matthieuvigne/MiAM_eurobot2018/Code_BBB/EurobotCode/src/Robot.c

#include "Robot.h"

// Define robot constants.
const double STEP_TO_SI = G_PI * 90.0 / 400.0;

const double ROBOT_WIDTH = 340;
const double CHASSIS_BACK = 145;
const double CHASSIS_FRONT = 145;
const double CHASSIS_SIDE = 155;
const double CANON_OFFSET = 103;
const double CLAW_OFFSET = 120;
const double MOUSE_SENSOR_OFFSET = 110;
const double BALL_LENGTH_OFFSET = 156;
const double BALL_WIDTH_OFFSET = 29;
const double BIN_OFFSET = 105;

const double GYRO_Z_BIAS = -0.00002;

const int RIGHT = 1;
const int LEFT = 0;

RobotPosition startingPosition = {0,0,0};

// Implementation of thread-safe robotPosition position and robotPosition target.
RobotPosition robotPosition;
GMutex positionMutex;

double robot_getPositionX()
{
	g_mutex_lock(&positionMutex);
	double x = robotPosition.x;
	g_mutex_unlock(&positionMutex);
	return x;
}

double robot_getPositionY()
{
	g_mutex_lock(&positionMutex);
	double Y = robotPosition.y;
	g_mutex_unlock(&positionMutex);
	return Y;
}

double robot_getPositionTheta()
{
	g_mutex_lock(&positionMutex);
	double t = robotPosition.theta;
	g_mutex_unlock(&positionMutex);
	return t;
}

void robot_setPositionX(double x)
{
	g_mutex_lock(&positionMutex);
	robotPosition.x = x;
	g_mutex_unlock(&positionMutex);
}

void robot_setPositionY(double y)
{
	g_mutex_lock(&positionMutex);
	robotPosition.y = y;
	g_mutex_unlock(&positionMutex);
}

void robot_setPositionTheta(double t)
{
	g_mutex_lock(&positionMutex);
	robotPosition.theta = t;
	g_mutex_unlock(&positionMutex);
}

void robot_setPosition(RobotPosition pos)
{
	g_mutex_lock(&positionMutex);
	robotPosition.x = pos.x;
	robotPosition.y = pos.y;
	robotPosition.theta = pos.theta;
	g_mutex_unlock(&positionMutex);
}

RobotPosition robot_getPosition()
{
	RobotPosition pos;
	g_mutex_lock(&positionMutex);
	pos.x = robotPosition.x;
	pos.y = robotPosition.y;
	pos.theta = robotPosition.theta;
	g_mutex_unlock(&positionMutex);
	return pos;
}
