matthieuvigne/MiAM_eurobot2018/Code_BBB/BBBEurobot/src/TCS3472ColorSensorDriver.c

#include "BBBEurobot/TCS3472ColorSensorDriver.h"
#include <math.h>
#include <stdio.h>

// Slave address: constant by chip reference.
// For TCS34725 and TCS34727 use 0x29.
// For TCS34721 and TCS34723 use 0x39.
const guint8 TCS3472_ADDRESS = 0x29;

const guint8 TCS3472_COMMAND_BIT = 0x80;

gboolean colorSensor_init(ColorSensorTCS3472 *sensor, I2CAdapter *adapter)
{
	if(adapter->file < 0)
		return FALSE;
	sensor->adapter = adapter;
	// Check chip identity.
	guint8 chipIdentity = i2c_readRegister(sensor->adapter, TCS3472_ADDRESS, TCS3472_COMMAND_BIT | 0x12);
	if(chipIdentity != 0x44 && chipIdentity != 0x4D)
	{
		printf("Error : TCS3472 not detected\n");
		return FALSE;
	}
	// Configure chip.
	// Set command register
	i2c_writeRegister(sensor->adapter, TCS3472_ADDRESS, TCS3472_COMMAND_BIT | 0x00, 0b10100000);

	// Set default integration time and gain.s
	colorSensor_setIntegrationTime(*sensor, 3);
	colorSensor_setGain(*sensor, TCS34725_GAIN_1X);
	// Enable chip.
	i2c_writeRegister(sensor->adapter, TCS3472_ADDRESS, TCS3472_COMMAND_BIT | 0x00, 0x01);
	// Wait 3ms for oscillator to start, then powerup the device.
	g_usleep(3000);
	i2c_writeRegister(sensor->adapter, TCS3472_ADDRESS, TCS3472_COMMAND_BIT | 0x00, 0x03);
	return TRUE;
}


gboolean colorSensor_setIntegrationTime(ColorSensorTCS3472 sensor, int integrationTime)
{
	// Compute register value.
	guint8 registerValue = (guint8) (256 - (floor(integrationTime / 2.4)));
	return i2c_writeRegister(sensor.adapter, TCS3472_ADDRESS, TCS3472_COMMAND_BIT | 0x01, registerValue);
}

gboolean colorSensor_setGain(ColorSensorTCS3472 sensor, TCS34725Gain_t gain)
{
	return i2c_writeRegister(sensor.adapter, TCS3472_ADDRESS, TCS3472_COMMAND_BIT | 0x0F, gain);
}

ColorOutput colorSensor_getData(ColorSensorTCS3472 sensor)
{
	ColorOutput color;
	guint8 sensorValue[8];
	i2c_readRegisters(sensor.adapter, TCS3472_ADDRESS, TCS3472_COMMAND_BIT | 0x14, 8, sensorValue);
	color.clear = (sensorValue[0] << 8) + sensorValue[1];
	color.red = (sensorValue[2] << 8) + sensorValue[3];
	color.green = (sensorValue[4] << 8) + sensorValue[5];
	color.blue = (sensorValue[6] << 8) + sensorValue[7];

	return color;
}
