matthieuvigne/MiAM_eurobot2018/Code_BBB/BBBEurobot/include/BBBEurobot/ADNS9800Firmware.h

// the firmeware that is uploaded in the ADNS each time it boots
#ifndef ADNS9800_FIRMWARE
#define ADNS9800_FIRMWARE
// Firmware "adns9800_srom_A4.txt" from 
// This firmware is Copyright Avago, please refer to them concerning modifications.

	const unsigned short firmware_length = 3070;
	uint8_t firmware_data[] = {
	0x03, 0xa4, 0x6e, 0x16, 0x6d, 0x89, 0x3e, 0xfe, 0x5f, 0x1c, 0xb8, 0xf2, 0x47, 0x0c, 0x7b, 
	0x74, 0x6a, 0x56, 0x0f, 0x7d, 0x76, 0x71, 0x4b, 0x0c, 0x97, 0xb6, 0xcf, 0xfd, 0x78, 0x72, 
	0x66, 0x2f, 0xbd, 0xf8, 0x53, 0x24, 0xab, 0xd4, 0x2c, 0xb0, 0xe4, 0x32, 0xf1, 0x6a, 0x56, 
	0x2e, 0xbf, 0xfc, 0x7a, 0x57, 0x0d, 0x79, 0x70, 0x66, 0x46, 0x0e, 0x7f, 0x5d, 0x19, 0x91, 
	0xaa, 0xc2, 0x0d, 0x8e, 0x7f, 0x5d, 0x19, 0xb0, 0xe2, 0x46, 0xef, 0x5c, 0x3a, 0xd7, 0x2c, 
	0xbb, 0xf4, 0x6a, 0x37, 0xcd, 0x18, 0xb2, 0xc7, 0x0c, 0x9a, 0x97, 0x8f, 0x52, 0xfd, 0x0d, 
	0xb8, 0x41, 0x00, 0x9e, 0x8e, 0x9a, 0x1e, 0x6d, 0x0c, 0xe2, 0xaa, 0x13, 0x93, 0xb8, 0xc1, 
	0x2a, 0x29, 0xbb, 0x0b, 0xe3, 0x71, 0x08, 0x6d, 0xfd, 0xb6, 0xd9, 0xcf, 0x65, 0x21, 0x27, 
	0x45, 0x1b, 0xbe, 0xe2, 0x61, 0x86, 0x3c, 0xbf, 0x68, 0x9c, 0xd6, 0x75, 0x01, 0x5e, 0xe0, 
	0xc6, 0x92, 0x79, 0xf4, 0x6a, 0xa9, 0xbb, 0x2a, 0x79, 0xd0, 0xe1, 0x5c, 0x32, 0xb1, 0x5a, 
	0x1b, 0xba, 0xaf, 0x11, 0xea, 0x24, 0x6a, 0x83, 0x4f, 0x8d, 0xed, 0x19, 0x62, 0x70, 0x54, 
	0xfb, 0x0e, 0x1f, 0x83, 0xcc, 0xf0, 0xb7, 0xae, 0x05, 0xd3, 0x42, 0x5d, 0x48, 0xa0, 0x7a, 
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
	0x46, 0xa7, 0xe2, 0xd3, 0x75, 0xff, 0x4f, 0x0c, 0x0c, 0xaf, 0xcd, 0xa6, 0x9c, 0xa6, 0x73, 
	0xe2, 0x6d, 0x17, 0x16, 0xb5, 0x99, 0x80, 0x35, 0xd9, 0x61, 0xf3, 0x48, 0x23, 0xff, 0xae, 
	0x53, 0x89, 0xfa, 0x55, 0x1c, 0x37, 0xa5, 0xe8, 0x62, 0x12, 0xb2, 0x22, 0x04, 0xed, 0x42, 
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

#endif
